tidklaas/Hephaistos-AHA/main/avm_aha.c

/*
 * This file is part of the Hephaistos-AHA project.
 * Copyright (C) 2018-2019  Tido Klaassen <tido_hephaistos@4gh.eu>
 *
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
 * You should have received a copy of the GNU General Public License
 * along with this program; if not, write to the Free Software
 * Foundation, Inc., 51 Franklin Street, Fifth Floor, Boston,
 * MA  02110-1301, USA.
 */

#include <string.h>
#include <stdlib.h>
#include <unistd.h>
#include <stdbool.h>
#include <sys/socket.h>
#include <errno.h>

#include <sdkconfig.h>

#include "freertos/FreeRTOS.h"
#include "freertos/event_groups.h"
#include "freertos/task.h"
#include "freertos/timers.h"
#include "esp_log.h"
#include "esp_system.h"
#include "esp_task_wdt.h"
#include "nvs_flash.h"

#include "lwip/err.h"
#include "lwip/sockets.h"
#include "lwip/sys.h"
#include "lwip/netdb.h"
#include "lwip/dns.h"

#include "mbedtls/platform.h"
#include "mbedtls/net_sockets.h"
#include "mbedtls/esp_debug.h"
#include "mbedtls/ssl.h"
#include "mbedtls/entropy.h"
#include "mbedtls/ctr_drbg.h"
#include "mbedtls/error.h"
#include "mbedtls/certs.h"
#include "mbedtls/md5.h"

#include <wifi_manager.h>
#include <expat.h>
#include <expat-dom.h>
#include <klist.h>
#include <kref.h>
#include <hephaistos.h>
#include <avm_aha.h>

#define TWDT_TIMEOUT_S  300
#define TASK_TIMER_S    5

static const char *TAG = "AHA";

static struct aha_cfg aha_cfg;
static SemaphoreHandle_t aha_cfg_lock = NULL;

static TaskHandle_t this = NULL;
static TimerHandle_t aha_timer = NULL;
static EventGroupHandle_t aha_event_group;

const int BIT_TIMER     = BIT0;
const int BIT_SUSPEND   = BIT1;
const int BIT_RELOAD    = BIT2;

static const char *HTTP_REQ = 
        "GET %s HTTP/1.0\r\n"
        "HOST: %s\r\n"
        "CONNECTION: keep-alive\r\n"
        "USER-AGENT: AVM UPnP/1.0 Client 1.0\r\n"
        "\r\n";

static const char *SID_CHECK = "/login_sid.lua?sid=%s";
static const char *SID_GET = "/login_sid.lua?username=%s&response=%s-%s";
static const char *HKR_REQ = "/webservices/homeautoswitch.lua?"
                             "switchcmd=getdevicelistinfos&sid=%s";

#define HTTP_REQ_SIZE   1024
#define INVALID_SID     "0000000000000000"

/*
 * Pointer to current aha_data available through aha_data_get().
 * Once initialised, will always hold a pointer to a valid data set.
 */
static struct aha_data *curr_aha_data = NULL;
static SemaphoreHandle_t aha_data_lock = NULL;
static volatile int data_created = 0;
static volatile int data_released= 0;

static struct aha_data *create_data(void)
{
    struct aha_data *data;

    data = calloc(sizeof(*data), 1);
    if(data == NULL){
        ESP_LOGE(TAG, "Out of memory for aha_data");
        goto on_exit;
    }

    kref_init(&(data->ref_cnt));
    INIT_KLIST_HEAD(&(data->dev_head));
    INIT_KLIST_HEAD(&(data->grp_head));
    data->heat_on = false;

    ++data_created;
    ESP_LOGD(TAG, "Data created: %d released: %d", data_created, data_released);

on_exit:
    return data;
}

static void release_data(struct kref *ref_cnt)
{
    struct aha_data *data;
    struct aha_device *device, *group, *tmp_dev, *tmp_grp;

    data = container_of(ref_cnt, struct aha_data, ref_cnt);

    klist_for_each_entry_safe(group, tmp_grp, &(data->grp_head), grp_list)
    {
        /* Remove all devices from the group's member list. */
        klist_for_each_entry_safe(device, tmp_dev,
                                  &(group->member_list), member_list)
        {
            klist_del(&(device->member_list));
            device->group = NULL;
        }

        /* Remove group from group list. */
        klist_del_init(&(group->grp_list));

        free(group);
    }

    klist_for_each_entry_safe(device, tmp_dev, &(data->dev_head), dev_list)
    {
        /* Remove device from device list. */
        klist_del(&(device->dev_list));
        free(device);
    }

    if(data->msg != NULL){
        free((void *) data->msg);
    }

    free(data);

    ++data_released;
    ESP_LOGD(TAG, "Data created: %d released: %d", data_created, data_released);
}

struct auth_data
{
    char user[AHA_CFG_MAXLEN];
    char pass[AHA_CFG_MAXLEN];
    char realm[128];
    char nonce[128];
    char auth[128];
    char sid[128];
};

int gen_tr064_auth(struct auth_data *data)
{
    mbedtls_md5_context ctx;
    unsigned char md5sum[16];
    unsigned char md5str[33];
    unsigned int i;

    memset(data->auth, 0x0, sizeof(data->auth));

    mbedtls_md5_init(&ctx);
    mbedtls_md5_starts(&ctx);
    mbedtls_md5_update(&ctx, (unsigned char *) data->user, strlen(data->user));
    mbedtls_md5_update(&ctx, (unsigned char *) ":", 1);
    mbedtls_md5_update(&ctx, (unsigned char *) data->realm,strlen(data->realm));
    mbedtls_md5_update(&ctx, (unsigned char *) ":", 1);
    mbedtls_md5_update(&ctx, (unsigned char *) data->pass, strlen(data->pass));
    mbedtls_md5_finish(&ctx, md5sum);
    mbedtls_md5_free(&ctx);

    for(i = 0; i < sizeof(md5sum); ++i){
        sprintf((char *) &(md5str[2 * i]), "%02x", md5sum[i]);
    }

    mbedtls_md5_init(&ctx);
    mbedtls_md5_starts(&ctx);
    mbedtls_md5_update(&ctx, md5str, 32);
    mbedtls_md5_update(&ctx, (unsigned char *) ":", 1);
    mbedtls_md5_update(&ctx, (unsigned char *)data->nonce, strlen(data->nonce));
    mbedtls_md5_finish(&ctx, md5sum);
    mbedtls_md5_free(&ctx);

    memset(data->auth, 0x0, sizeof(data->auth));
    for(i = 0; i < sizeof(md5sum); ++i){
        sprintf(&(data->auth[2 * i]), "%02x", md5sum[i]);
    }

    return 0;
}

int gen_sid_auth(struct auth_data *data)
{
    mbedtls_md5_context ctx;
    unsigned char md5sum[16];
    unsigned char buf[256];
    unsigned int i, curr;
    int result;

    result = 0;
    memset(data->auth, 0x0, sizeof(data->auth));

    /*
     * Auth request is the hex string of md5-sum of UTF-16LE string
     * "<nonce>-<password>", where characters must be in the ISO-8859-1
     * range... m(
     */
    if(sizeof(buf) < 2 * (strlen(data->nonce) + strlen(data->pass) + 1)){
        ESP_LOGE(TAG, "[%s] Auth data too big.", __func__);
        result = -EINVAL;
        goto on_exit;
    }

    curr = 0;
    memset(buf, 0x0, sizeof(buf));
    for(i = 0; i < strlen(data->nonce); ++i){
        buf[curr] = data->nonce[i];
        curr += 2;
    }

    buf[curr] = '-';
    curr += 2;

    for(i = 0; i < strlen(data->pass); ++i){
        buf[curr] = data->pass[i];
        curr += 2;
    }

    mbedtls_md5_init(&ctx);
    mbedtls_md5_starts(&ctx);
    mbedtls_md5_update(&ctx, (unsigned char *) buf, curr);
    mbedtls_md5_finish(&ctx, md5sum);
    mbedtls_md5_free(&ctx);

    memset(data->auth, 0x0, sizeof(data->auth));
    for(i = 0; i < sizeof(md5sum); ++i){
        sprintf(&(data->auth[2 * i]), "%02x", md5sum[i]);
    }

on_exit:
    return result;
}

static int do_http_req(char *host, char *service, dom_t **dom, const char *req)
{
    char buf[64];
    char *reply;
    size_t written, len, offset;
    void *dom_parser;
    int body, result, sock, tmp;
    struct addrinfo hints;
    struct addrinfo *info;
    struct timeval receiving_timeout;

    sock = -1;
    info = NULL;
    *dom = NULL;
    dom_parser = NULL;
    errno = 0;

    memset(&hints, 0x0, sizeof(hints));
    hints.ai_family = AF_INET;
    hints.ai_socktype = SOCK_STREAM;

    result = getaddrinfo(host, service, &hints, &info);
    if(result != 0 || info == NULL){
        ESP_LOGE(TAG, "DNS lookup failed err=%d (%s) info=%p",
                   result, strerror(errno), info);
        goto on_exit;
    }

    sock = socket(info->ai_family, info->ai_socktype, 0);
    if(sock < 0){
        ESP_LOGE(TAG, "[%s] Failed to allocate socket: %s",
                   __func__, strerror(errno));
        result = sock;
        goto on_exit;
    }

    result = connect(sock, info->ai_addr, info->ai_addrlen);
    if(result != 0){
        ESP_LOGE(TAG, "[%s] socket connect failed: %s",
                   __func__, strerror(errno));
        goto on_exit;
    }

    written = 0;
    len = strlen(req);
    while(len > 0){
        result = write(sock, &(req[written]), len);
        if(result < 0){
            ESP_LOGE(TAG, "[%s] socket send failed: %s",
                       __func__, strerror(errno));
            goto on_exit;
        }
        written += result;
        len -= result;
    }

    receiving_timeout.tv_sec = 5;
    receiving_timeout.tv_usec = 0;
    result = setsockopt(sock, SOL_SOCKET, SO_RCVTIMEO, &receiving_timeout,
                          sizeof(receiving_timeout));
    if(result < 0){
        ESP_LOGE(TAG, "[%s] setsockopt() failed: %s",
                   __func__, strerror(errno));
        goto on_exit;
    }

    body = 0;
    offset = 0;
    do{
        /*
         * Read data chunks from socket. The end-of-header marker might be
         * spread over multiple reads, so the parser below will tell us the
         * offset into the read buffer.
         */
        len = sizeof(buf) - offset;
        memset(&(buf[offset]), 0x0, sizeof(buf) - offset);
        errno = 0;
        result = read(sock, (unsigned char *) &(buf[offset]), len);
        if(result < 0){
            ESP_LOGE(TAG, "[%s] read() failed: %s", __func__, strerror(errno));
            goto on_exit;
        }

        /* Connection closed? */
        if(result == 0){
            break;
        }

        /* We received some data. Set up pointer to buffer and adjust length. */
        len = result + offset;
        reply = buf;

        if(body == 0){
            /*
             * We are looking for "\r\n\r\n" which separates HTTP header and
             * body.
             */

            reply = memmem(buf, len, "\r\n\r\n", 4);
            if(reply == NULL){
                /*
                 * Due to chunked reads we can not rely on the separator being
                 * received completely in one read. Therefore we move the last
                 * three bytes to the start of the buffer and continue reading
                 * from the socket.
                 */
                memmove(buf, &(buf[len - 3]), 3);
                offset = 3;
            } else {
                /*
                 * We found the start of the HTTP body. Adjust reply pointer
                 * and data length so the rest of the reply can be fed to the
                 * XML parser.
                 */
                reply += 4;
                len -= (reply - buf);
                offset = 0;
                body = 1;
            }
        }

        if(body == 1){
            result = dom_parse_chunked_data(&dom_parser, dom, reply, len, 0);
            if(result != 0){
                ESP_LOGE(TAG, "[%s] Incremental parse failed: %d",
                          __func__, result);
                goto on_exit;
            }
        }
    }while(1);

on_exit:
    /*
     * If we started parsing XML data, we have to make sure that the parsing
     * gets finalised. Just calling XML_ParserFree() instead results in a
     * serious memory leak.
     */
    if(dom_parser != NULL){
        tmp = dom_parse_chunked_data(&dom_parser, dom, NULL, 0, 1);
        if(tmp != 0){
            ESP_LOGE(TAG, "[%s] Final parse failed: %d", __func__, result);
            if(result == 0){
                result = tmp;
            }
        }
    }

    if(info != NULL){
        freeaddrinfo(info);
    }

    if(sock >= 0){
        errno = 0;
        tmp = close(sock);
        if(tmp != 0){
            ESP_LOGE(TAG, "[%s] close() failed: %s", __func__, strerror(errno));
        }
    }

    /* Release any (partial) DOM on error and make sure we return NULL. */
    if(result != 0 && *dom != NULL){
        ESP_LOGE(TAG, "[%s] Freeing dom", __func__);
        dom_free(*dom);
        *dom = NULL;
    }

    return result;
}

static int parse_attr_ul(dom_t *dom, const char *name, unsigned long *dst)
{
    int result;
    const char *val;

    result = 0;
    val = dom_find_attr(dom->attr, name);
    if(val == NULL){
        result = -ENOENT;
        goto on_exit;
    }

    errno = 0;
    *dst = strtoul(val, NULL, 10);
    result = errno;

on_exit:
    return result;
}

static int __attribute__((unused))
parse_attr_long(dom_t *dom, const char *name, long *dst)
{
    int result;
    const char *val;

    result = 0;
    val = dom_find_attr(dom->attr, name);
    if(val == NULL){
        result = -ENOENT;
        goto on_exit;
    }

    errno = 0;
    *dst = strtol(val, NULL, 10);
    result = errno;

on_exit:
    return result;
}

static int parse_data_ul(dom_t *dom, const char *name, unsigned long *dst)
{
    int result;
    dom_t *node;
    char buf[32];

    result = 0;
    node = dom_find_node(dom, name);
    if(node == NULL){
        result = -ENOENT;
        goto on_exit;
    }

    if(node->data_len >= (sizeof(buf) - 1)){
        result = -EINVAL;
        goto on_exit;
    }

    memcpy(buf, node->data, node->data_len);
    buf[node->data_len] = '\0';

    errno = 0;
    *dst = strtoul(buf, NULL, 10);
    result = errno;

on_exit:
    return result;
}

static int parse_data_long(dom_t *dom, const char *name, long *dst)
{
    int result;
    dom_t *node;
    char buf[32];

    result = 0;
    node = dom_find_node(dom, name);
    if(node == NULL){
        result = -ENOENT;
        goto on_exit;
    }

    if(node->data_len >= (sizeof(buf) - 1)){
        result = -ENOSPC;
        goto on_exit;
    }

    memcpy(buf, node->data, node->data_len);
    buf[node->data_len] = '\0';

    errno = 0;
    *dst = strtol(buf, NULL, 10);
    result = errno;

on_exit:
    return result;
}

static int copy_attr_str(dom_t *dom, const char *name, char *dst, size_t len)
{
    const char *attr;
    size_t written;
    int result;

    result = 0;
    attr = dom_find_attr(dom->attr, name);
    if(attr == NULL){
        result = -ENOENT;
        goto on_exit;
    }

    written = strlcpy(dst, attr, len);
    if(written >= len){
        result = -ENOSPC;
    }

on_exit:
    return result;
}

static int copy_data_str(dom_t *dom, const char *name, char *dst, size_t len)
{
    dom_t *node;
    int result;

    result = 0;
    node = dom_find_node(dom, name);
    if(node == NULL){
        result = -ENOENT;
        goto on_exit;
    }

    if(node->data_len >= len){
        result = -ENOSPC;
        goto on_exit;
    }

    memcpy(dst, node->data, node->data_len);
    dst[node->data_len] = '\0';

on_exit:
    return result;
}

static int
parse_lock_state(dom_t *dom, const char *name, enum aha_lock_mode *state)
{
    unsigned long tmp;
    int result;

    result = parse_data_ul(dom, name, &tmp);
    if(result == 0){
        switch(tmp){
        case 0:
            *state = aha_lock_off;
            break;
        case 1:
            *state = aha_lock_on;
            break;
        default:
            result = -EINVAL;
            goto on_exit;
        }
    }

on_exit:
    return result;
}

static int
parse_switch_state(dom_t *dom, const char *name, enum aha_switch_state *state)
{
    unsigned long tmp;
    int result;

    result = parse_data_ul(dom, name, &tmp);
    if(result == 0){
        switch(tmp){
        case 0:
            *state = aha_swstate_off;
            break;
        case 1:
            *state = aha_swstate_on;
            break;
        default:
            result = -EINVAL;
            goto on_exit;
        }
    }

on_exit:
    return result;
}

static int compare_data_str(dom_t *dom, const char *name, const char *val)
{
    dom_t *node;
    int result;

    result = 0;
    node = dom_find_node(dom, name);
    if(node == NULL){
        result = -ENOENT;
        goto on_exit;
    }

    if(strncasecmp(val, node->data, node->data_len) != 0){
        result = 1;
    }

on_exit:
    return result;
}

static int
parse_switch_mode(dom_t *dom, const char *name, enum aha_switch_mode *mode)
{
    int result;

    result = compare_data_str(dom, name, "auto");
    if(result < 0){
        result = -EINVAL;
        goto on_exit;
    } else if(result == 0){
        *mode = aha_switch_auto;
        goto on_exit;
    }

    result = compare_data_str(dom, name, "manuell");
    if(result < 0){
        result = -EINVAL;
        goto on_exit;
    } else if(result == 0){
        *mode = aha_switch_manual;
        goto on_exit;
    }

    result = -ENOENT;

on_exit:
    return result;
}

static int parse_group_entry(dom_t *dom, struct aha_device *entry)
{
    dom_t *node;
    char buf[AHA_ENTRY_LEN];
    char *tok, *saveptr;
    unsigned long val;
    int result;

    result = 0;
    node = dom_find_node(dom, "groupinfo");
    if(node == NULL){
        goto on_exit;
    }

    node = node->child;

    result = parse_data_ul(node, "masterdeviceid", &(entry->grp.master_dev));
    if(result != 0 && result != -ENOENT){
        ESP_LOGE(TAG, "Parsing masterdeviceid failed for entry %s",
                 entry->name);
        goto on_exit;
    }
    result = 0;

    result = copy_data_str(node, "members", buf, sizeof(buf));
    if(result != 0){
        ESP_LOGE(TAG, "Copying member string failed for entry %s", entry->name);
        result = -EINVAL;
        goto on_exit;
    }

    tok = strtok_r(buf, ",", &saveptr);
    while(tok != NULL
          && entry->grp.member_cnt < ARRAY_SIZE(entry->grp.members))
    {
        errno = 0;
        val = strtoul(tok, NULL, 10);
        if(errno != 0){
            ESP_LOGE(TAG, "Error parsing group members for entry %s",
                     entry->name);
            result = errno;
            goto on_exit;
        }

        entry->grp.members[entry->grp.member_cnt] = val;
        ++entry->grp.member_cnt;
        tok = strtok_r(NULL, ",", &saveptr);
    }

    entry->grp.present = true;

on_exit:
    return result;
}

static int parse_hkr_entry(dom_t *dom, struct aha_device *entry)
{
    dom_t *node;
    int result;

    result = 0;
    node = dom_find_node(dom, "hkr");
    if(node == NULL){
        goto on_exit;
    }

    node = node->child;

    result = parse_data_ul(node, "tist", &(entry->hkr.act_temp));
    if(result != 0){
        ESP_LOGE(TAG, "Error parsing actual temperature for entry %s",
                 entry->name);
        goto on_exit;
    }

    result = parse_data_ul(node, "tsoll", &(entry->hkr.set_temp));
    if(result != 0){
        ESP_LOGE(TAG, "Error parsing set temperature for entry %s",
                 entry->name);
        goto on_exit;
    }

    result = parse_data_ul(node, "komfort", &(entry->hkr.comfort_temp));
    if(result != 0){
        ESP_LOGE(TAG, "Error parsing comfort temperature for entry %s",
                 entry->name);
        goto on_exit;
    }

    result = parse_data_ul(node, "absenk", &(entry->hkr.eco_temp));
    if(result != 0){
        ESP_LOGE(TAG, "Error parsing eco temperature for entry %s",
                 entry->name);
        goto on_exit;
    }

    result = parse_data_ul(node, "errorcode", &(entry->hkr.error));
    if(result != 0){
        ESP_LOGE(TAG, "Error parsing error code for entry %s", entry->name);
        goto on_exit;
    }

    if(dom_find_node(node, "battery")){
        result = parse_data_ul(node, "battery", &(entry->hkr.batt_level));
        if(result != 0){
            ESP_LOGE(TAG, "Error parsing battery level for entry %s",
                       entry->name);
            goto on_exit;
        }
    } else {
        entry->hkr.batt_level = 100;
    }

    if(dom_find_node(node, "batterylow")){
        result = parse_data_ul(node, "batterylow", &(entry->hkr.batt_low));
        if(result != 0){
            ESP_LOGE(TAG, "Error parsing battery status for entry %s",
                       entry->name);
            goto on_exit;
        }
    } else {
        entry->hkr.batt_low = 0;
    }

    if(dom_find_node(node, "summeractive")){
        result = parse_data_ul(node, "summeractive",
                               &(entry->hkr.summer_act));
        if(result != 0){
            ESP_LOGE(TAG, "Error parsing summer status for entry %s",
                       entry->name);
            goto on_exit;
        }
    } else {
        entry->hkr.summer_act = 0;
    }

    if(dom_find_node(node, "holidayactive")){
        result = parse_data_ul(node, "holidayactive",
                               &(entry->hkr.holiday_act));
        if(result != 0){
            ESP_LOGE(TAG, "Error parsing holiday status for entry %s",
                       entry->name);
            goto on_exit;
        }
    } else {
        entry->hkr.holiday_act = 0;
    }

    if(dom_find_node(node, "windowopenactiv")){
        result = parse_data_ul(node, "windowopenactiv",
                               &(entry->hkr.window_open));
        if(result != 0){
            ESP_LOGE(TAG, "Error parsing holiday status for entry %s",
                       entry->name);
            goto on_exit;
        }
    } else {
        entry->hkr.window_open = 0;
    }

    result = parse_data_ul(node, "endperiod", &(entry->hkr.next_change));
    if(result != 0){
        ESP_LOGE(TAG, "Error parsing next change time for entry %s",
                 entry->name);
        goto on_exit;
    }

    result = parse_data_ul(node, "tchange", &(entry->hkr.next_temp));
    if(result != 0){
        ESP_LOGE(TAG, "Error parsing next change temperature for entry %s",
                 entry->name);
        goto on_exit;
    }

    result = parse_lock_state(node, "lock", &(entry->hkr.lock));
    if(result != 0){
        ESP_LOGE(TAG, "Error parsing hkr lock state for entry %s", entry->name);
        goto on_exit;
    }

    result = parse_lock_state(node, "devicelock", &(entry->hkr.device_lock));
    if(result != 0){
        ESP_LOGE(TAG, "Error parsing hkr device lock state for entry %s",
                 entry->name);
        goto on_exit;
    }

    entry->hkr.present = true;

on_exit:
    return result;
}

static int parse_swi_entry(dom_t *dom, struct aha_device *entry)
{
    dom_t *node;
    int result;

    result = 0;
    node = dom_find_node(dom, "switch");
    if(node == NULL){
        goto on_exit;
    }

    node = node->child;

    result = parse_switch_state(dom, "state", &(entry->swi.state));
    if(result != 0){
        ESP_LOGE(TAG, "Error parsing switch state for entry %s", entry->name);
        goto on_exit;

    }

    result = parse_switch_mode(dom, "mode", &(entry->swi.mode));
    if(result != 0){
        ESP_LOGE(TAG, "Error parsing switch state for entry %s", entry->name);
        goto on_exit;

    }

    result = parse_lock_state(node, "lock", &(entry->swi.lock));
    if(result != 0){
        ESP_LOGE(TAG, "Error parsing switch lock state for entry %s",
                 entry->name);
        goto on_exit;
    }

    result = parse_lock_state(node, "devicelock", &(entry->swi.device_lock));
    if(result != 0){
        ESP_LOGE(TAG, "Error parsing switch device lock state for entry %s",
                 entry->name);
        goto on_exit;
    }

    entry->swi.present = true;

on_exit:
    return result;
}

static int parse_pwr_entry(dom_t *dom, struct aha_device *entry)
{
    dom_t *node;
    int result;

    result = 0;
    node = dom_find_node(dom, "powermeter");
    if(node == NULL){
        goto on_exit;
    }

    node = node->child;

    result = parse_data_ul(node, "power", &(entry->pwr.power));
    if(result != 0){
        ESP_LOGE(TAG, "Error parsing power for entry %s", entry->name);
        goto on_exit;
    }

    result = parse_data_ul(node, "energy", &(entry->pwr.energy));
    if(result != 0){
        ESP_LOGE(TAG, "Error parsing energy for entry %s", entry->name);
        goto on_exit;
    }

    entry->pwr.present = true;

on_exit:
    return result;
}

static int parse_temp_entry(dom_t *dom, struct aha_device *entry)
{
    dom_t *node;
    int result;

    result = 0;
    node = dom_find_node(dom, "temperature");
    if(node == NULL){
        goto on_exit;
    }

    node = node->child;

    result = parse_data_long(node, "celsius", &(entry->temp.temp_c));
    if(result != 0){
        ESP_LOGE(TAG, "Error parsing temperature for entry %s", entry->name);
        goto on_exit;
    }

    result = parse_data_long(node, "offset", &(entry->temp.offset));
    if(result != 0){
        ESP_LOGE(TAG, "Error parsing temperature offset for entry %s",
                 entry->name);
        goto on_exit;
    }

    entry->temp.present = true;

on_exit:
    return result;
}

static struct aha_device *parse_entry(dom_t *dom)
{
    struct aha_device *entry;
    int result;

    result = 0;
    entry = NULL;

    entry = calloc(1, sizeof(*entry));
    if(entry == NULL){
        ESP_LOGE(TAG, "Out of memory parsing device.");
        result = -ENOMEM;
        goto on_exit;
    }

    INIT_KLIST_HEAD(&(entry->dev_list));
    INIT_KLIST_HEAD(&(entry->grp_list));
    INIT_KLIST_HEAD(&(entry->member_list));

    if(!strcasecmp(dom->name, "device")){
        entry->type = aha_type_device;
    }else if(!strcasecmp(dom->name, "group")){
        entry->type = aha_type_group;
    }else{
        ESP_LOGE(TAG, "Invalid entry type %s", dom->name);
        result = -EINVAL;
        goto on_exit;
    }

    result = copy_data_str(dom, "name", entry->name, sizeof(entry->name));
    if(result != 0){
        ESP_LOGE(TAG, "Parsing entry name failed");
        goto on_exit;
    }

    result = copy_attr_str(dom, "identifier", entry->identifier,
                           sizeof(entry->identifier));
    if(result != 0){
        ESP_LOGE(TAG, "Parsing identifier failed for entry %s", entry->name);
        goto on_exit;
    }

    result = copy_attr_str(dom, "fwversion", entry->fw_version,
                           sizeof(entry->fw_version));
    if(result != 0){
        ESP_LOGE(TAG, "Parsing fwversion failed for entry %s", entry->name);
        goto on_exit;
    }

    result = copy_attr_str(dom, "manufacturer", entry->manufacturer,
                           sizeof(entry->manufacturer));
    if(result != 0){
        ESP_LOGE(TAG, "Parsing manufacturer failed for entry %s", entry->name);
        goto on_exit;
    }

    result = copy_attr_str(dom, "productname", entry->product_name,
                           sizeof(entry->product_name));
    if(result != 0){
        ESP_LOGE(TAG, "Parsing productname failed for entry %s", entry->name);
        goto on_exit;
    }

    result = parse_attr_ul(dom, "id", &(entry->id));
    if(result != 0){
        ESP_LOGE(TAG, "Parsing ID failed for entry %s", entry->name);
        goto on_exit;
    }

    result = parse_attr_ul(dom, "functionbitmask", &(entry->functions));
    if(result != 0){
        ESP_LOGE(TAG, "Parsing functions failed for entry %s", entry->name);
        goto on_exit;
    }

    result = parse_data_ul(dom->child, "present", &(entry->present));
    if(result != 0){
        ESP_LOGE(TAG, "Parsing present state failed for entry %s", entry->name);
        goto on_exit;
    }

    result = parse_group_entry(dom->child, entry);
    if(result != 0){
        ESP_LOGE(TAG, "Parsing group info failed for entry %s", entry->name);
        goto on_exit;
    }

    result = parse_hkr_entry(dom->child, entry);
    if(result != 0){
        ESP_LOGE(TAG, "Parsing hkr info failed for entry %s", entry->name);
        goto on_exit;
    }

    result = parse_swi_entry(dom->child, entry);
    if(result != 0){
        ESP_LOGE(TAG, "Parsing switch info failed for entry %s", entry->name);
        goto on_exit;
    }

    result = parse_pwr_entry(dom->child, entry);
    if(result != 0){
        ESP_LOGE(TAG, "Parsing powermeter info failed for entry %s",
                 entry->name);
        goto on_exit;
    }

    result = parse_temp_entry(dom->child, entry);
    if(result != 0){
        ESP_LOGE(TAG, "Parsing thermometer info failed for entry %s",
                 entry->name);
        goto on_exit;
    }

on_exit:
    if(result != 0 && entry != NULL){
        free(entry);
        entry = NULL;
    }

    return entry;
}


static struct aha_data *parse_dom(dom_t *dom)
{
    dom_t *node, *entry;
    struct aha_device *device, *group;
    struct aha_data *data;
    unsigned int idx;
    int result;

    result = 0;

    data = create_data();
    if(data == NULL){
        result = -ENOMEM;
        goto on_exit;
    }

    node = dom_find_node(dom, "devicelist");
    if(node == NULL){
        result = -ENOENT;
        goto on_exit;
    }

    /*
     * We parse the DOM in two passes. On the first pass we only handle
     * group entries. This makes sure that all groups are already in the
     * group-list when we start parsing the "real" devices.
     */
    entry = dom_find_node(node->child, "group");
    while(entry != NULL){
        device = parse_entry(entry);
        if(device != NULL){
            klist_add_tail(&(device->grp_list), &(data->grp_head));
        }
        entry = dom_find_node(entry->next, "group");
    }

    /*
     * Second pass for the "real" devices. We need to check the entries
     * in the group-list to see if this device is a member of that group.
     */
    entry = dom_find_node(node->child, "device");
    while(entry != NULL){
        device = parse_entry(entry);
        if(device != NULL){
            klist_add_tail(&(device->dev_list), &(data->dev_head));

            /*
             * Loop over all groups and their members until we either
             * find a match or run out of groups to check.
             */
            klist_for_each_entry(group, &(data->grp_head), grp_list)
            {
                for(idx = 0; idx < group->grp.member_cnt; ++idx){
                    if(device->id == group->grp.members[idx]){
                        device->group = group;
                        klist_add_tail(&(device->member_list),
                                          &(group->member_list));
                        break;
                    }
                }

                /* Match found, no need to continue. */
                if(device->group != NULL){
                    break;
                }
            }
        }

        entry = dom_find_node(entry->next, "device");
    }
    
on_exit:
    if(result != 0 && data != NULL){
        aha_data_release(data);
        data = NULL;
    }

    return data;
}

static void dump_hkr(struct aha_hkr *hkr, const char *prefix)
{
    if(hkr->present){
        ESP_LOGD(TAG,
                 "%s[HKR] Set: %lu Act: %lu Comf: %lu Eco: %lu Next: %lu "
                 "Change: %lu: Batt: %lu BattLow: %lu Win: %lu Holiday: %lu "
                 "Summer: %lu Lock: %s DevLock: %s Err: %lu",
                 prefix,
                 hkr->set_temp,
                 hkr->act_temp,
                 hkr->comfort_temp,
                 hkr->eco_temp,
                 hkr->next_temp,
                 hkr->next_change,
                 hkr->batt_level,
                 hkr->batt_low,
                 hkr->window_open,
                 hkr->holiday_act,
                 hkr->summer_act,
                 hkr->lock == aha_lock_on ? "on" : "off",
                 hkr->device_lock == aha_lock_on ? "on" : "off",
                 hkr->error);
    }
}

static void dump_swi(struct aha_switch *swi, const char *prefix)
{
    if(swi->present){
        ESP_LOGD(TAG, "%s[SWI] State: %s Mode: %s Lock: %s DevLock: %s",
                 prefix,
                 swi->state == aha_swstate_on ? "on" : "off",
                 swi->mode == aha_switch_auto ? "auto" : "manual",
                 swi->lock == aha_lock_on ? "on" : "off",
                 swi->device_lock == aha_lock_on ? "on" : "off");
    }
}

static void dump_temp(struct aha_thermo *tmp, const char *prefix)
{
    if(tmp->present){
        ESP_LOGD(TAG, "%s[TMP] Temperature: %ld Offset: %ld",
                 prefix,
                 tmp->temp_c,
                 tmp->offset);
    }
}

static void dump_pwr(struct aha_power *pwr, const char *prefix)
{
    if(pwr->present){
        ESP_LOGD(TAG, "%s[PWR] Power: %lu Energy: %lu",
                 prefix,
                 pwr->power,
                 pwr->energy);
    }
}

static void dump_device(struct aha_device *dev, const char *prefix)
{
    ESP_LOGD(TAG, "%s[%s] Name: %s ID: %lu Present: %lu Ident: %s FW: %s "
                  "Manuf: %s ProdName: %s Funcs: 0x%lx",
             prefix,
             dev->type == aha_type_device ? "DEV" : "GRP",
             dev->name,
             dev->id,
             dev->present,
             dev->identifier,
             dev->fw_version,
             dev->manufacturer,
             dev->product_name,
             dev->functions);

    dump_hkr(&(dev->hkr), prefix);
    dump_swi(&(dev->swi), prefix);
    dump_temp(&(dev->temp), prefix);
    dump_pwr(&(dev->pwr), prefix);

}

static void dump_data(struct aha_data *data)
{
    struct aha_device *dev, *grp;

    /* Skip traversing data if nothing is going to be printed anyways. */
    if(LOG_LOCAL_LEVEL < ESP_LOG_DEBUG){
        goto on_exit;
    }

    /* Dump groups and its member devices. */
    klist_for_each_entry(grp, &(data->grp_head), grp_list){
        dump_device(grp, "");
        klist_for_each_entry(dev, &(grp->member_list), member_list){
            dump_device(dev, " -> ");
        }
    }

    /* Dump remaining devices not belonging to a group. */
    klist_for_each_entry(dev, &(data->dev_head), dev_list){
        if(dev->group == NULL){
            dump_device(dev, "");
        }
    }

on_exit:
    return;
}

static int check_auth(struct auth_data *auth)
{
    char buf[128];
    char *req;
    dom_t *dom, *node;
    int result, written;

    result = 0;
    req = NULL;
    dom = NULL;

    req = calloc(1, HTTP_REQ_SIZE);
    if(req == NULL){
        ESP_LOGE(TAG, "Out of memory for request");
        result = -ENOMEM;
        goto on_exit;
    }

    written = snprintf(buf, sizeof(buf), SID_CHECK, auth->sid);
    if(written >= sizeof(buf)){
        ESP_LOGE(TAG, "SID check too big");
        result = -EINVAL;
        goto on_exit;
    }

    written = snprintf(req, HTTP_REQ_SIZE, HTTP_REQ, buf, aha_cfg.fbox_port);
    if(written >= HTTP_REQ_SIZE){
        ESP_LOGE(TAG, "HTTP SID check too big");
        result = -EINVAL;
        goto on_exit;
    }

    result = do_http_req(aha_cfg.fbox_addr, aha_cfg.fbox_port, &dom, req);
    if(result != 0){
        ESP_LOGE(TAG, "HTTP SID check failed");
        goto on_exit;
    }

    node = dom_find_node(dom, "SID");
    if(node && strncmp(node->data, INVALID_SID, node->data_len)){
        ESP_LOGD(TAG, "SID %s still valid", auth->sid);
        goto on_exit;
    }

    result = copy_data_str(dom, "Challenge", auth->nonce, sizeof(auth->nonce));
    if(result != 0){
        goto on_exit;
    }

    result = gen_sid_auth(auth);
    if(result != 0){
        ESP_LOGE(TAG, "Generating auth response failed.");
        goto on_exit;
    }

    dom_free(dom);
    dom = NULL;

    memset(req, 0x0, HTTP_REQ_SIZE);
    written = snprintf(buf, sizeof(buf), SID_GET, auth->user, auth->nonce,
                        auth->auth);
    if(written >= sizeof(buf)){
        ESP_LOGE(TAG, "SID request too big");
        result = -EINVAL;
        goto on_exit;
    }

    written = snprintf(req, HTTP_REQ_SIZE, HTTP_REQ, buf, aha_cfg.fbox_addr);
    if(written >= HTTP_REQ_SIZE){
        ESP_LOGE(TAG, "HTTP SID request too big");
        result = -EINVAL;
        goto on_exit;
    }

    result = do_http_req(aha_cfg.fbox_addr, aha_cfg.fbox_port, &dom, req);
    if(result != 0){
        ESP_LOGE(TAG, "HTTP SID request failed");
        goto on_exit;
    }

    result = copy_data_str(dom, "SID", auth->sid, sizeof(auth->sid));
    if(result != 0 || !strcmp(auth->sid, INVALID_SID)){
        ESP_LOGE(TAG, "Unable to retrieve valid SID");
        result = -EPERM;
        goto on_exit;
    }

    ESP_LOGD(TAG, "New SID: %s", auth->sid);

on_exit:
    if(req != NULL){
        free(req);
    }

    if(dom != NULL){
        dom_free(dom);
    }

    return result;
}

static dom_t *fetch_data(struct auth_data *auth)
{
    char buf[128];
    char *req;
    dom_t *dom;
    int result, written;

    result = 0;
    req = NULL;
    dom = NULL;

    req = calloc(1, HTTP_REQ_SIZE);
    if(req == NULL){
        ESP_LOGE(TAG, "[%s]Out of memory for HTTP AHA request", __func__);
        result = -ENOMEM;
        goto on_exit;
    }

    written = snprintf(buf, sizeof(buf), HKR_REQ, auth->sid);
    if(written >= sizeof(buf)){
        ESP_LOGE(TAG, "[%s]HTTP AHA request too big", __func__);
        result = -EINVAL;
        goto on_exit;
    }

    written = snprintf(req, HTTP_REQ_SIZE, HTTP_REQ, buf, aha_cfg.fbox_addr);
    if(written >= HTTP_REQ_SIZE){
        ESP_LOGE(TAG, "[%s]HTTP AHA data request too big", __func__);
        result = -EINVAL;
        goto on_exit;
    }

    result = do_http_req(aha_cfg.fbox_addr, aha_cfg.fbox_port, &dom, req);
    if(result != 0){
        ESP_LOGE(TAG, "[%s]HTTP AHA data request failed", __func__);
        goto on_exit;
    }

on_exit:
    if(result != 0 && dom != NULL){
        dom_free(dom);
        dom = NULL;
    }

    if(req != NULL){
        free(req);
    }

    return dom;
}

static enum aha_heat_mode dev_needs_heat(struct aha_device *dev)
{
    enum aha_heat_mode result;
    struct aha_hkr *hkr;
    time_t now;

    hkr = &(dev->hkr);

    /* Default to off. */
    result = aha_heat_off;

    /* Ignore if this is not a hkr. */
    if(hkr->present == false){
        goto on_exit;
    }

    if(hkr->set_temp == HEAT_FORCE_ON){
        result = aha_heat_on;
        goto on_exit;
    }

    if(hkr->set_temp == HEAT_FORCE_OFF){
        result = aha_heat_off;
        goto on_exit;
    }

    /* F!Box sometimes provides bogus temperature data after reboot. */
    if(hkr->act_temp == 0){
        result = aha_heat_off;
        goto on_exit;
    }

    /*
     * Do not change heat mode if the target temparature will be set lower than
     * the current actual temperature within the hysteresis time span.
     */
    time(&now);
    if((hkr->act_temp >= hkr->next_temp)
        && ((hkr->next_change - now) <= CONFIG_HYSTERESIS))
    {
        result = aha_heat_keep;
        goto on_exit;
    }

    /*
     * No imminent target temperature change ahead, just compare actual and
     * target temperature.
     */
    if(hkr->act_temp < hkr->set_temp){
        result = aha_heat_on;
    }

on_exit:
    return result;
}

static enum aha_heat_mode need_heat(struct aha_data *data,
                                    enum aha_heat_mode mode)
{
    struct aha_device *device;
    enum aha_heat_mode result, tmp;

    result = aha_heat_off;

    if(data == NULL){
        goto on_exit;
    }

    klist_for_each_entry(device, &(data->dev_head), dev_list){
        tmp = dev_needs_heat(device);
        if(tmp == aha_heat_on){
            /*
             * If heater is going to be turned on, print device(s) that caused
             * the change.
             */
            if(mode != aha_heat_on){
                ESP_LOGI(TAG,"Needs Heat: %s", device->name);
            }

            data->heat_on = true;
        }

        result = LWIP_MAX(tmp, result);
    }

    /* Only print updates on heater state when things actually change. */
    if(result != aha_heat_keep && result != mode){
        ESP_LOGI(TAG, "Fire %s!", data->heat_on ? "on" : "off");
    }

on_exit:
    return result;
}

static void timer_cb(TimerHandle_t timer)
{
    xEventGroupSetBits(aha_event_group, BIT_TIMER);
}

esp_err_t aha_set_cfg(struct aha_cfg *cfg, bool reload)
{
    esp_err_t result;
    nvs_handle handle;

    if(aha_cfg_lock == NULL){

        return ESP_ERR_TIMEOUT;
    }

    result = nvs_open(AHA_NVS_NAMESPC, NVS_READWRITE, &handle);
    if(result != ESP_OK){
        return result;
    }

    if(xSemaphoreTake(aha_cfg_lock, 100 * portTICK_PERIOD_MS) != pdTRUE){
        result = ESP_ERR_TIMEOUT;
        goto on_exit;
    }

    result = nvs_set_str(handle, "fbox_user", cfg->fbox_user);
    if(result != ESP_OK){
        goto on_exit_unlock;
    }

    result = nvs_set_str(handle, "fbox_pass", cfg->fbox_pass);
    if(result != ESP_OK){
        goto on_exit_unlock;
    }

    result = nvs_set_str(handle, "fbox_addr", cfg->fbox_addr);
    if(result != ESP_OK){
        goto on_exit_unlock;
    }

    result = nvs_set_str(handle, "fbox_port", cfg->fbox_port);
    if(result != ESP_OK){
        goto on_exit_unlock;
    }

    result = nvs_commit(handle);
    if(result != ESP_OK){
        goto on_exit_unlock;
    }

    if(reload){
        xEventGroupSetBits(aha_event_group, BIT_RELOAD);
    }

on_exit_unlock:
    xSemaphoreGive(aha_cfg_lock);

on_exit:
    nvs_close(handle);

    return result;
}

esp_err_t aha_get_cfg(struct aha_cfg *cfg, enum cfg_load_type from)
{
    esp_err_t result;
    size_t len;
    nvs_handle handle;

    if(from != cfg_ram && from != cfg_nvs){
        return ESP_ERR_INVALID_ARG;
    }

    if(aha_cfg_lock == NULL){
        return ESP_ERR_TIMEOUT;
    }

    if(from == cfg_nvs){
        result = nvs_open(AHA_NVS_NAMESPC, NVS_READONLY, &handle);
        if(result != ESP_OK){
            return result;
        }
    }

    if(xSemaphoreTake(aha_cfg_lock, 100 * portTICK_PERIOD_MS) != pdTRUE){
        result = ESP_ERR_TIMEOUT;
        goto on_exit;
    }

    if(from == cfg_ram){
        memmove(cfg, &aha_cfg, sizeof(*cfg));
        result = ESP_OK;
        goto on_exit_unlock;
    }

    memset(cfg, 0x0, sizeof(*cfg));

    len = sizeof(cfg->fbox_user);
    result = nvs_get_str(handle, "fbox_user", cfg->fbox_user, &len);
    if(result != ESP_OK){
        goto on_exit_unlock;
    }

    len = sizeof(cfg->fbox_pass);
    result = nvs_get_str(handle, "fbox_pass", cfg->fbox_pass, &len);
    if(result != ESP_OK){
        goto on_exit_unlock;
    }

    len = sizeof(cfg->fbox_addr);
    result = nvs_get_str(handle, "fbox_addr", cfg->fbox_addr, &len);
    if(result != ESP_OK){
        goto on_exit_unlock;
    }

    len = sizeof(cfg->fbox_port);
    result = nvs_get_str(handle, "fbox_port", cfg->fbox_port, &len);
    if(result != ESP_OK){
        goto on_exit_unlock;
    }

on_exit_unlock:
    xSemaphoreGive(aha_cfg_lock);

on_exit:
    if(from == cfg_nvs){
        nvs_close(handle);
    }

    return result;
}

struct aha_data *aha_data_get(void)
{
    struct aha_data *data;

    data = NULL;
    if(aha_data_lock == NULL || curr_aha_data == NULL){
        goto on_exit;
    }

    if(xSemaphoreTake(aha_data_lock, 100 * portTICK_PERIOD_MS) == pdTRUE){
        kref_get(&(curr_aha_data->ref_cnt));
        data = curr_aha_data;
        xSemaphoreGive(aha_data_lock);
    }

on_exit:
    return data;
}

void aha_data_release(struct aha_data *data)
{
    if(data != NULL){
        kref_put(&(data->ref_cnt), release_data);
    }
}

void aha_task_suspend(void)
{
    if(aha_event_group != NULL){
        xEventGroupSetBits(aha_event_group, BIT_SUSPEND);
        (void) esp_task_wdt_delete(this);
    }
}

void aha_task_resume(void)
{
    if(aha_event_group != NULL){
        xEventGroupClearBits(aha_event_group, BIT_SUSPEND);
        (void) esp_task_wdt_add(this);
    }
}

void avm_aha_task(void *pvParameters)
{
    int result;
    struct auth_data auth_data;
    struct aha_data *old_data, *new_data;
    enum aha_heat_mode heat_mode;
    dom_t *dom;
    EventBits_t events;

    this = xTaskGetCurrentTaskHandle();

    result = esp_task_wdt_init(TWDT_TIMEOUT_S, true);
    if(result != 0){
        ESP_LOGE(TAG, "[%s]WDT setup failed.", __func__);
        goto on_exit;
    }

    aha_data_lock = xSemaphoreCreateMutex();
    if(aha_data_lock == NULL){
        ESP_LOGE(TAG, "[%s]Creating aha_data_lock failed.", __func__);
        goto on_exit;
    }

    aha_cfg_lock = xSemaphoreCreateMutex();
    if(aha_cfg_lock == NULL){
        ESP_LOGE(TAG, "[%s]Creating aha_cfg_lock failed.", __func__);
        goto on_exit;
    }

    aha_event_group = xEventGroupCreate();
    if(aha_event_group == NULL){
        ESP_LOGE(TAG, "[%s]Creating aha_event_group failed.", __func__);
        goto on_exit;
    }

    /*
     * Force main loop to wait until released from main task.
     * Also trigger reloading of config from NVS.
     */
    xEventGroupSetBits(aha_event_group, (BIT_SUSPEND | BIT_RELOAD));

    aha_timer = xTimerCreate("AHA_Timer", pdMS_TO_TICKS(5000), pdTRUE,
                             NULL, timer_cb);

    if(aha_timer == NULL){
        ESP_LOGE(TAG, "[%s]Creating aha_timer failed.", __func__);
        goto on_exit;
    }

    result = xTimerStart(aha_timer, portMAX_DELAY);
    if(result == pdFAIL){
        ESP_LOGE(TAG, "[%s]Starting aha_timer failed.", __func__);
        goto on_exit;
    }

    srand(esp_get_free_heap_size());
    heat_mode = aha_heat_off;

    do{
        /* Wait for and clear timer bit. */
        events = xEventGroupWaitBits(aha_event_group, BIT_TIMER,
                                     true, false, portMAX_DELAY);

        if(events & BIT_RELOAD){
            /*
             * Clear the reload bit before trying to load the config.
             * This way we will not miss a reload if an update happens
             * immediately after aha_get_cfg() releases the config mutex.
             */
            xEventGroupClearBits(aha_event_group, BIT_RELOAD);

            result = aha_get_cfg(&aha_cfg, cfg_nvs);
            if(result == ESP_OK){
                ESP_LOGI(TAG, "Config reloaded");

                memset(&auth_data, 0x0, sizeof(auth_data));

                strlcpy(auth_data.user, aha_cfg.fbox_user,
                        sizeof(auth_data.user));

                strlcpy(auth_data.pass, aha_cfg.fbox_pass,
                        sizeof(auth_data.pass));

            } else {
                ESP_LOGW(TAG, "Config reload failed");

                /* Make sure we try again. */
                xEventGroupSetBits(aha_event_group, BIT_RELOAD);
                continue;
            }
        }

        if(events & BIT_SUSPEND){
            ESP_LOGD(TAG, "Task suspended");
            continue;
        }

        result = esp_task_wdt_reset();
        if(result != 0){
            ESP_LOGE(TAG, "WDT reset failed.");
            goto on_exit;
        }

        /* Skip data retrieval if we have connectivity or network issues. */
        if(!esp_wmngr_is_connected()){
            continue;
        }

        /* Everything seems to be in order. Try fetching a new data set. */
        heph_led_set(true);
        
        result = check_auth(&auth_data);
        if(result != 0){
            continue;
        }

        ESP_LOGD(TAG, "Free heap before fetch: 0x%x", esp_get_free_heap_size());
        dom = fetch_data(&auth_data);
        ESP_LOGD(TAG, "Free heap after fetch: 0x%x", esp_get_free_heap_size());
        if(dom == NULL){
            ESP_LOGW(TAG, "Fetching data failed");
            continue;
        }

        ESP_LOGD(TAG, "Free heap before parse: 0x%x", esp_get_free_heap_size());
        new_data = parse_dom(dom);
        dom_free(dom);
        ESP_LOGD(TAG, "Free heap after parse: 0x%x", esp_get_free_heap_size());
        if(new_data == NULL){
            ESP_LOGE(TAG, "Parsing data failed");
            continue;
        }

        time(&(new_data->timestamp));
        new_data->msg = strdup("Don't Panic!");
        dump_data(new_data);

        /* We have a new data set. Analyse it and update heater control. */
        heat_mode = need_heat(new_data, heat_mode);

        heph_led_set(false);

        ESP_LOGD(TAG, "Free heap before data update: 0x%x", esp_get_free_heap_size());

        /* Try to update public aha state data. */
        if(xSemaphoreTake(aha_data_lock, 100 * portTICK_PERIOD_MS) == pdTRUE){
            old_data = curr_aha_data;
            curr_aha_data = new_data;
            if(old_data != NULL){
                if(heat_mode == aha_heat_keep){
                    new_data->heat_on = old_data->heat_on;
                }
                aha_data_release(old_data);
            }
            xSemaphoreGive(aha_data_lock);
        } else {
            ESP_LOGW(TAG, "Unable to get aha_data_lock for update.");
            aha_data_release(new_data);
        }

        if(curr_aha_data != NULL && heat_mode != aha_heat_keep){
            heph_heat_set(curr_aha_data->heat_on);
        }

        ESP_LOGD(TAG, "Free heap after data update: 0x%x", esp_get_free_heap_size());
    }while(1);

on_exit:
    while(1)
        ;

    return;
}
